susesKaninchen/KittenExplode/Master/data/img/0kjMcUe.jpg

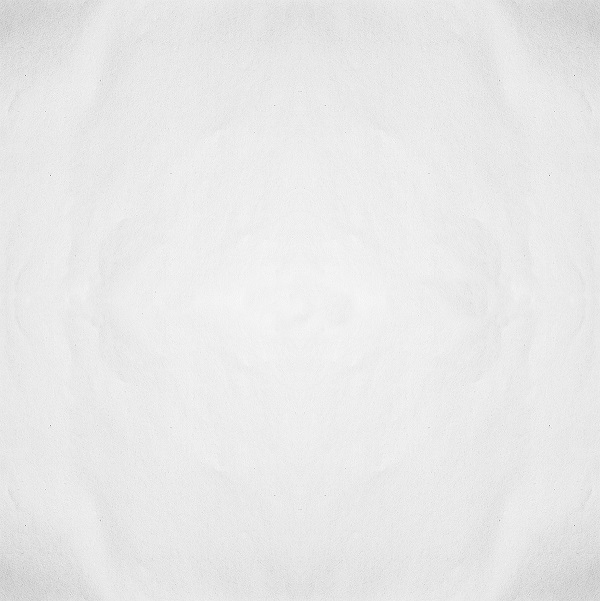
Master/data/img/0kjMcUe.jpg
